baprozeniuk/ESP8266TempLogger/collector.py

import socket #for listening for packets
import sys #general use
import traceback #for debug traces
import time #for file and screen logging
import binascii #for packet decoding
import struct #for packet decoding
import boto3 #for Amazon SNS
from email.MIMEMultipart import MIMEMultipart #for email
from email.MIMEText import MIMEText #for email
import smtplib #for email
import psycopg2 #for postgres
import json

errorlog = ""       

def sendEmail(toaddr,fromaddr,server,port,subject,body,TLS,username,password):
   try:
      #compose email
      msg = MIMEMultipart()
      msg['From'] = fromaddr
      msg['To'] = toaddr
      msg['Subject'] = subject
      msg.attach(MIMEText(body,'plain'))
      #send email
      server = smtplib.SMTP(server,port)
      server.ehlo()
      if TLS == True:
         server.starttls()
         server.login(username,password)
      server.sendmail(fromaddr, toaddr, msg.as_string())
      server.quit()
   except:
      file = open(errorlog,"a")
      file.write("Error Sending Email\n")
      err = traceback.format_exc()
      file.write(err)
      file.close()
      print "Error Sending Email", err
      
def sendSMS(SNS,phoneNumber,topic_arn,message):
   try:
      SNS.subscribe(
      TopicArn=topic_arn,
      Protocol='sms',
      Endpoint=phoneNumber
      )  
      SNS.publish(
      Message=message,
      TopicArn=topic_arn
      )      
   except:
      err = traceback.format_exc()
      file = open(errorlog,"a")
      file.write("Error Sending SMS\n")
      file.write(err)
      file.close()
      print "Error Sending SMS", err  
      
def logToDB(dbname,dbuser,dbhost,dbpass,mac,id,value):
   try: #try to connect to database
      connstr = "dbname='%s' user='%s' host='%s' password='%s'" % (dbname,dbuser,dbhost,dbpass)
      conn = psycopg2.connect(connstr)
      cursor = conn.cursor()
   except:
      err = traceback.format_exc()
      file = open(errorlog,"a")
      file.write("Error Connecting to Database\n")
      file.write(err)
      file.close()
      print "Error Connecting to Database\n", err   
   try: #try to insert a record
      cursor.execute("INSERT INTO esp_log (sample_host, sample_id, sample_value) VALUES (%s,%s,%s)", (mac,id,value))
      conn.commit()
      cursor.close()
      conn.close()
   except UnboundLocalError:
      file = open(errorlog,"a")
      file.write("Error: Database Not Connected\n")
      err = traceback.format_exc()
      file.write(err)
      file.close()
      print "Error: Database Not Connected\n", err
   except:
      file = open(errorlog,"a")
      file.write("Error: Unhandled Database Exception\n")
      err = traceback.format_exc()
      file.write(err)
      file.close()
      print "Error: Unhandled Database Exception\n", err      
            
            
def main():
   
   with open('config.json', 'r') as f:
      config = json.load(f)
   #all config loads from a json file. Override only for debugging
   #file logging settings
   logfile = config['file_config']['logfile']
   global errorlog
   errorlog = config['file_config']['errorfile']
   
   #email settings 
   email = config['email_config']['enable']
   TLS = config['email_config']['tls'] 
   fromaddr = config['email_config']['fromaddr']
   toaddr = config['email_config']['toaddr']
   euser = config['email_config']['user']
   epassword = config['email_config']['password']
   smtp_server = config['email_config']['smtp_server']
   smtp_port = config['email_config']['smtp_port']

   #SMS settings
   SMS = config['sns_config']['enable'] #enable or disable SMS notification
   phoneNumber = config['sns_config']['phonenumber']
   aws_key_id = config['sns_config']['aws_key_id']
   aws_secret_key = config['sns_config']['aws_secret_key']
   aws_topic = config['sns_config']['aws_topic']
   
   #alerting ranges 'sensor MAC': (minC,maxC)
   ranges = {'2c3ae80ac099': (25,43), 
             '6001944f0482': (20,25)}

   #where to listen for packets
   UDP_IP = config['server_config']['ip']
   UDP_PORT = config['server_config']['port']

   sock = socket.socket(socket.AF_INET,socket.SOCK_DGRAM)
   sock.bind((UDP_IP, UDP_PORT))
   #database settings:
   database = config['db_config']['enable']
   dbname = config['db_config']['dbname']
   dbhost = config['db_config']['dbhost']
   dbuser = config['db_config']['dbuser']
   dbpass = config['db_config']['dbpass']
   #setup objects for sending SMS via Amazon SNS
   if SMS == True:
      SNS = boto3.client(
          "sns",
          aws_access_key_id=aws_key_id,
          aws_secret_access_key=aws_secret_key,
          region_name="us-east-1"
      )
      # Create the topic if it doesn't exist
      topic = SNS.create_topic(Name=aws_topic)
      topic_arn = topic['TopicArn']  # get its Amazon Resource Name

   while True: #main loop
      #wait for data
      data, addr = sock.recvfrom(1024)
      #decode packet
      databytes = bytearray(data)
      serial = bytearray(6)
      id = bytearray(2)
      value = bytearray(4)
      for i in range(0,6):
         serial[i] = databytes[i]
      for i in range(6,8):
         id[i-6] = databytes[i]
      for i in range (8,12):
         value[i-8] = databytes[i]
      #convert decoded formats
      serial_str = binascii.b2a_hex(serial)
      id_str = binascii.b2a_hex(id)
      b = ''.join(chr(i) for i in value)
      value_float = struct.unpack('>f', b)[0]
      value_str = binascii.b2a_hex(value)
      #compose a line to log
      line = ("%s,%s,%s,%s\n" % (time.time(), serial_str, id_str, value_float))
      #write line to screen
      print line
      #write to log
      file = open(logfile,"a")
      file.write(line)
      file.close()
      #write to db
      if database == True:
         logToDB(dbname,dbuser,dbhost,dbpass,serial_str,id,value_float)      
      try:
         if (value_float > config['sensor_ranges'][serial_str]['high']) or (value_float < config['sensor_ranges'][serial_str]['low']): #if the current value is out of the acceptable range, alert
            print "Alert! Temperature out of range!"
            if email == True:
               subject = "Sensor Alert"
               body = ("Alert! Sensor Out of range! \nCurrent Sensor Reading for sensor id %s is %s\n" % (serial_str, value_float))
               sendEmail(toaddr,fromaddr,smtp_server,smtp_port,subject,body,TLS,euser,epassword)               
            if SMS == True:
               message = ("Alert! Sensor Out of range! \nCurrent Sensor Reading for sensor id %s is %s\n" % (serial_str, value_float))
               sendSMS(SNS,phoneNumber,topic_arn,message)
      except KeyError:
         err = "Warning: Sensor %s:%s does not have a configured range\n" % (serial_str, id_str)
         print err
         file = open(errorlog,"a")
         file.write(err)
         file.close()
     
if __name__ == '__main__':
   sys.exit(main())  
